CascoLogix/LaunchPad_3x7-Segment_Booster_Pack/Rendered_Pics/LaunchPad_3x7-Segment_Display_Booster_Pack_Top_ISO2.png

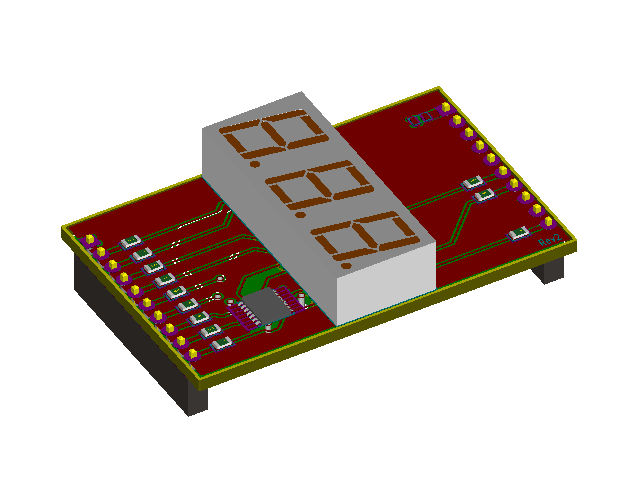
Rendered_Pics/LaunchPad_3x7-Segment_Display_Booster_Pack_Top_ISO2.png
