CascoLogix/LaunchPad_3x7-Segment_Booster_Pack/Hardware/KiCAD_Project_Files/LaunchPad_3x7-Segment_Display_Booster_Pack.sch

## KiCad design Hardware/KiCAD_Project_Files/LaunchPad_3x7-Segment_Display_Booster_Pack.sch (2013-12-04, an earlier design)

Schematic: LaunchPad_3x7-Segment_Display_Booster_Pack.sch

Parts:
C1: 10uF
P1, P2: HEADER_1X10
R1, R2, R3, R4, R5, R6, R7, R8, R9, R10, R11, R12: 100
U1: 74LS125
U2: LTC4624

Notes on the sheet:
LaunchPad 3x7-Segment Display Booster Pack
